pwr235728/AudioLocator/audio_direction/ltspice/model.asc

C1: cap; 33p
C2: cap; 2µ
C3: cap; 1µ
C4: cap; 1µ
C5: cap; 2µ
C6: cap; 33p
R1: res; 4k7
R2: res; 90k; tol=5
R3: res; 10k
R4: res; 47k
R5: res; 47k
R6: res; 100k
R7: res; 47k
R8: res; 90k; tol=5
R9: res; 10k
U1: OP07
U2: OP07
V1: voltage; 5
V2: voltage; 0
V3: voltage; SINE(0 0.01 100 0 0 0 100); AC 0.01
V4: voltage; 5
Named nets: 0, 10v, -10v, out, vin
.ac dec 10000 1 100000
;tran 0 100m 0 100u
