pwr235728/AudioLocator/SoundAngleStm32/Inc/audio_locator_conf.h

/*
 * sound_dir_conf.h
 *
 *  Created on: 13.10.2019
 *      Author: proxima
 */

#ifndef SOUND_DIR_CONF_H_
#define SOUND_DIR_CONF_H_


#define SAMPLE_RATE 20000
#define SAMPLE_BUFFER_DURATION_MS 200 // 100ms

#define TEST_FREQUENCY 	1000	// Hz
#define SOUND_SPEED 	340.3	// m/s
#define DISPLACEMENT 	0.0127 	// m

#define SAMPLE_BUFFER_LEN  SAMPLE_RATE*SAMPLE_BUFFER_DURATION_MS/1000


#endif /* SOUND_DIR_CONF_H_ */
